cristianoag/obsonet/labels/Label_Obsonet_patola_72x51.jpg

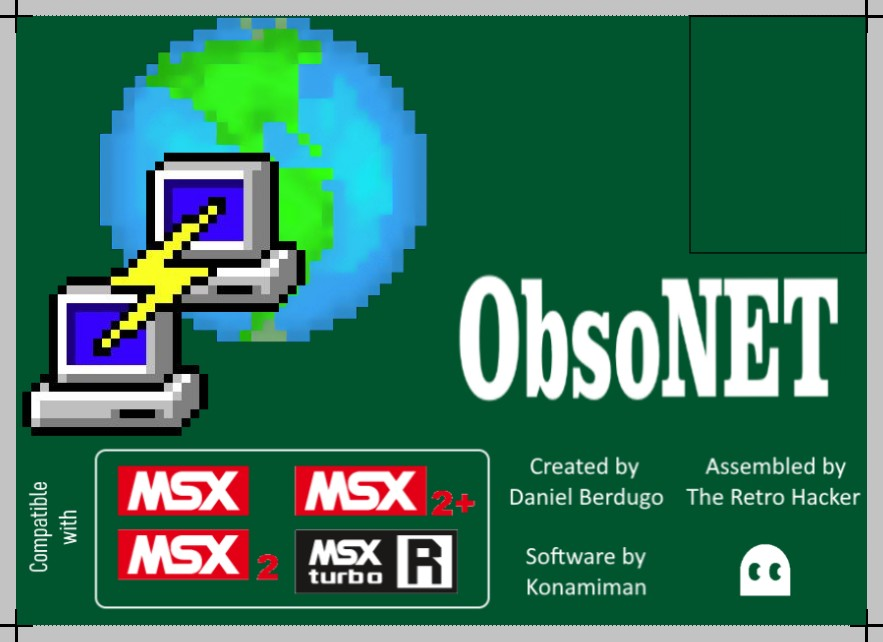
labels/Label_Obsonet_patola_72x51.jpg
