cristianoag/obsonet/labels/Label_Obsonet_Patola_Top_89x12.png

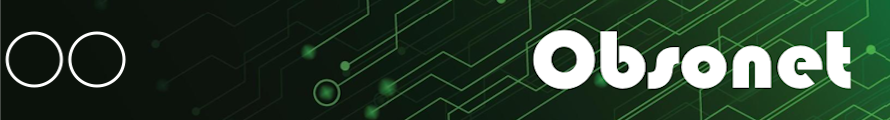
labels/Label_Obsonet_Patola_Top_89x12.png
